jeremynguyenn/Accumulator_Electronics/Accumulator_Electronics/Accumulator Base/CAD Models/Accumulator Box/ARCOL_HS100-220R J.stp

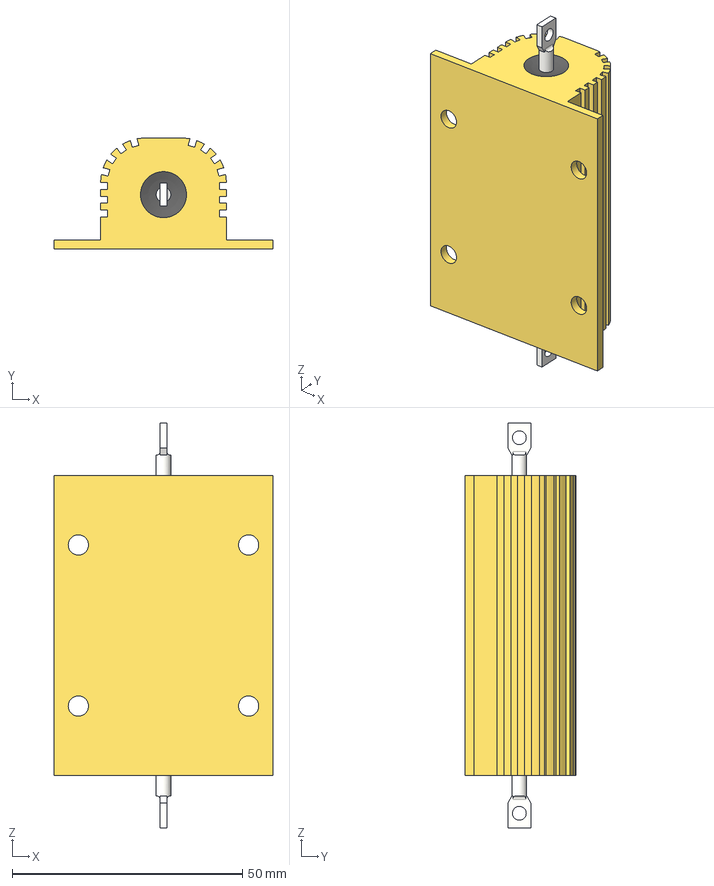
[picture p13: CAD file, 2025-11-17]
Accumulator_Electronics/Accumulator Base/CAD Models/Accumulator Box/ARCOL_HS100-220R J.stp
47.5 x 24.1 x 88.0 mm
