jeremynguyenn/Accumulator_Electronics/Accumulator_Electronics/AIL+TSAL Shield/TSAL_Simulation/TSAL AIL.asc

AIL: diode; 1N914
C1: cap; 10µ
C2: cap; 10p
D1: diode; 1N914
D2: diode; 1N914
M1: nmos; IRF7201
M2: pmos; IRF7205
R1: res; 10k
R2: res; 10k
R3: res; 2k
R4: res; 20k
R6: res; 10k
R7: res; 10k
R8: res; 2k
R9: res; 2k
R10: res; 650
U1: opamp2; LM393
U2: NE555
V1: voltage; PULSE(0 12 0 0 0 2 )
V2: voltage; 12
Named nets: DCDC, GLV-Battery, 0, Select, Red, Green
.include LM393.5_1
.tran 0 10 1p 1
R6 and R7 probably not needed, can test in real life.
R8 and R9 not needed in real life.
(The TSALs we use have an internal resistance)
TSAL Circuitry
Last updated 7-9-2020 
Bert Steyaert and Sabin Zarrandikoetxea
Warning: purchase these exact transistor and OpAmp models
